Fightingbox/Flatbox-LED-Mirrored/pictures/assets/5.jpg

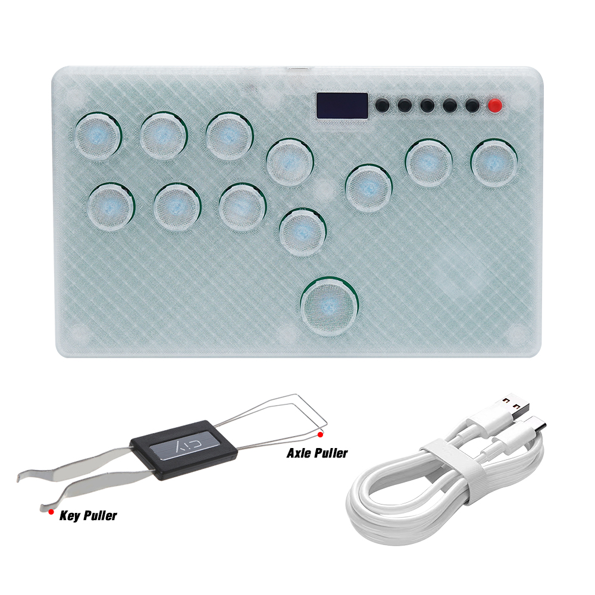
pictures/assets/5.jpg
