Fightingbox/Flatbox-LED-Mirrored/software/configs/BentoBox/assets/ScrubTier_Large.png

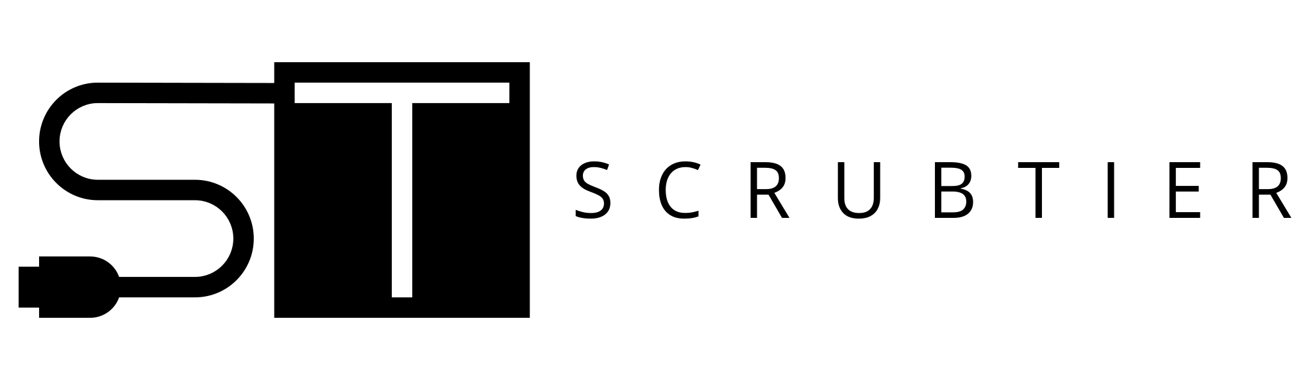
software/configs/BentoBox/assets/ScrubTier_Large.png
