Fightingbox/Flatbox-LED-Mirrored/software/configs/BentoBox/assets/ST_BentoBoxV1.png

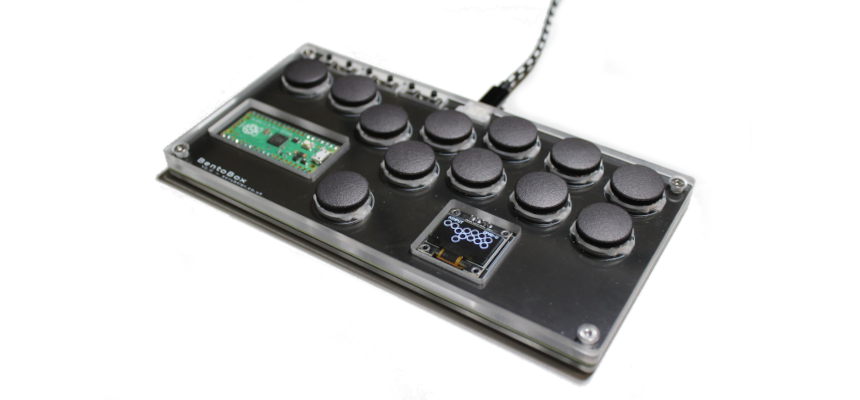
software/configs/BentoBox/assets/ST_BentoBoxV1.png
