Fightingbox/Flatbox-LED-Mirrored/software/configs/BentoBox/assets/ST_BentoBoxV2.png

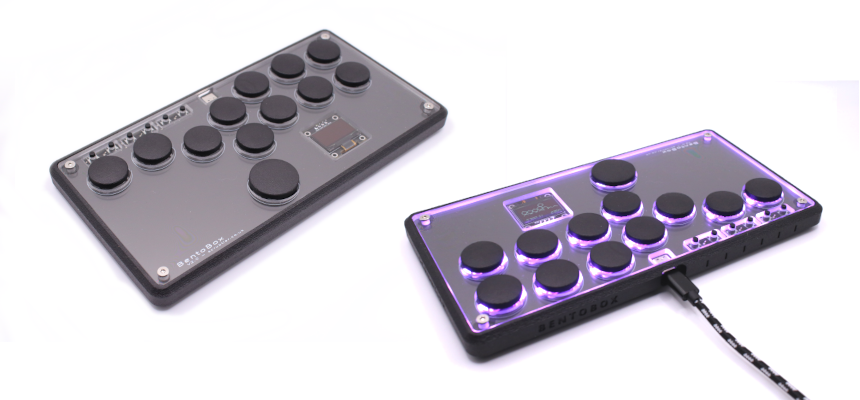
software/configs/BentoBox/assets/ST_BentoBoxV2.png
