Fightingbox/Flatbox-LED-Mirrored/software/configs/BentoBox/assets/ST_GGEZStick.png

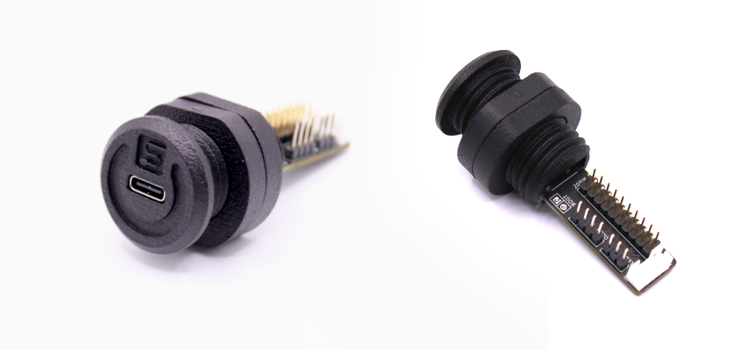
software/configs/BentoBox/assets/ST_GGEZStick.png
