Fightingbox/Flatbox-LED-Mirrored/software/configs/DuelPad-S001/assets/Flatbox-rev2b-finished-product.jpg

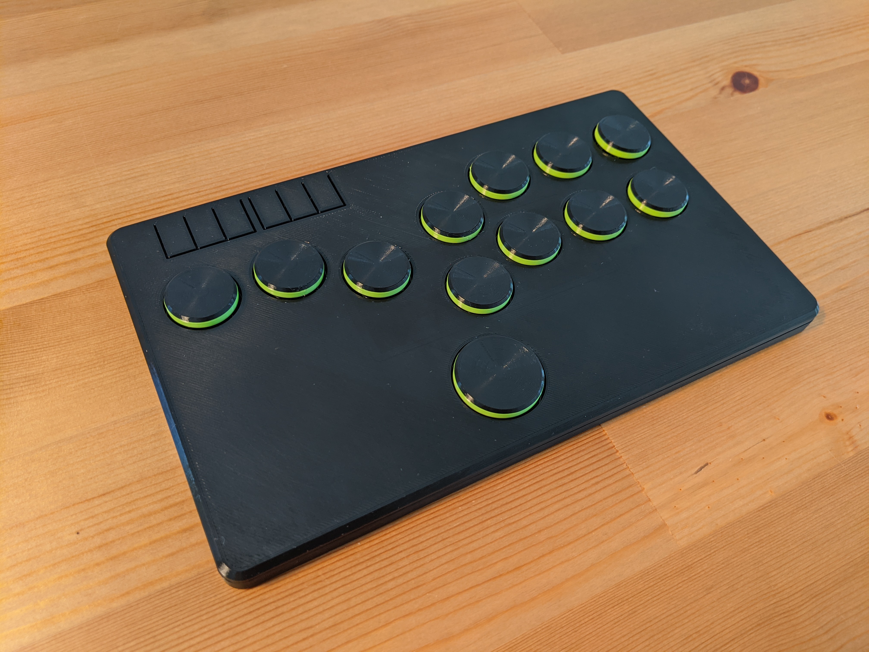
software/configs/DuelPad-S001/assets/Flatbox-rev2b-finished-product.jpg
