Fightingbox/Flatbox-LED-Mirrored/software/configs/FightboardV3/assets/FightboardV3.jpg

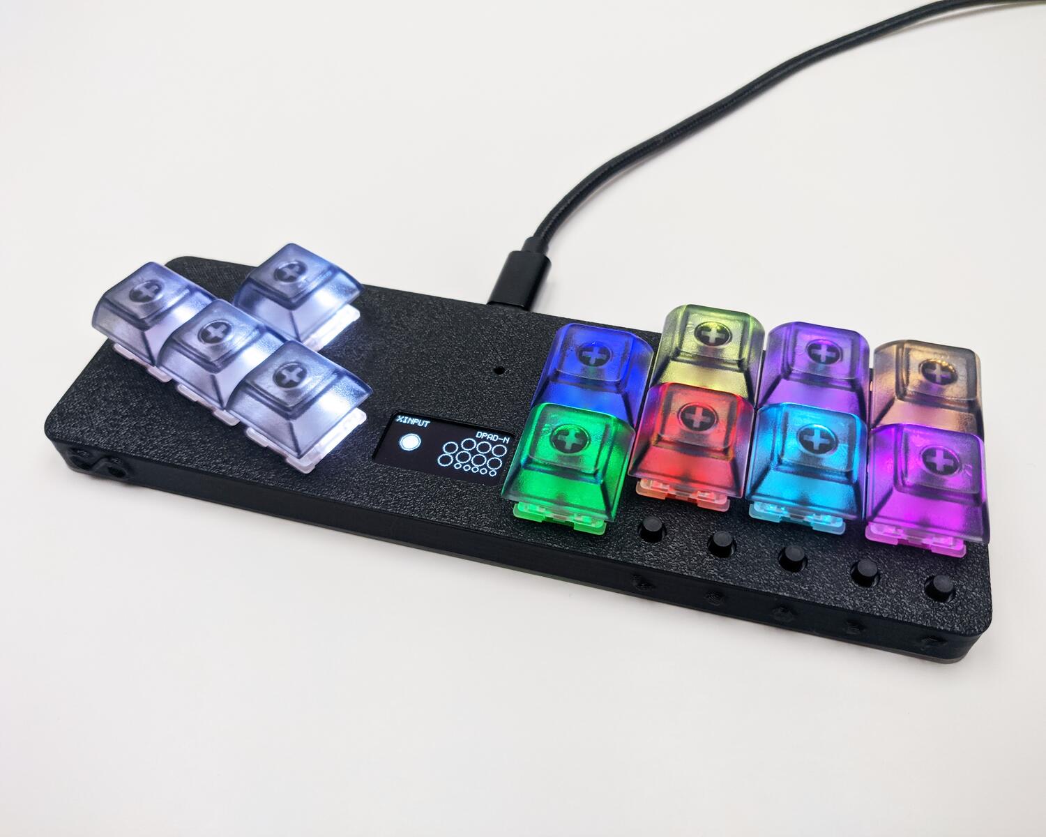
software/configs/FightboardV3/assets/FightboardV3.jpg
