Fightingbox/Flatbox-LED-Mirrored/software/configs/FightboardV3Mirrored/assets/FightboardV3Mirrored.jpg

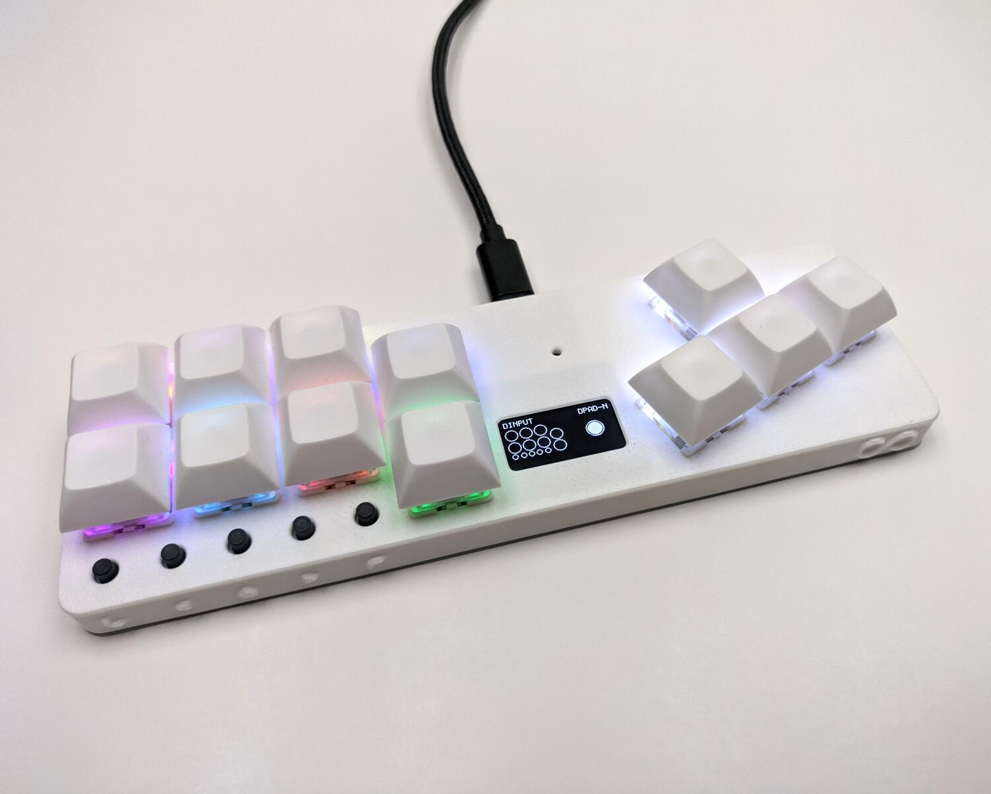
software/configs/FightboardV3Mirrored/assets/FightboardV3Mirrored.jpg
