Fightingbox/Flatbox-LED-Mirrored/software/configs/FlatboxRev5/assets/Flatbox-rev5.jpg

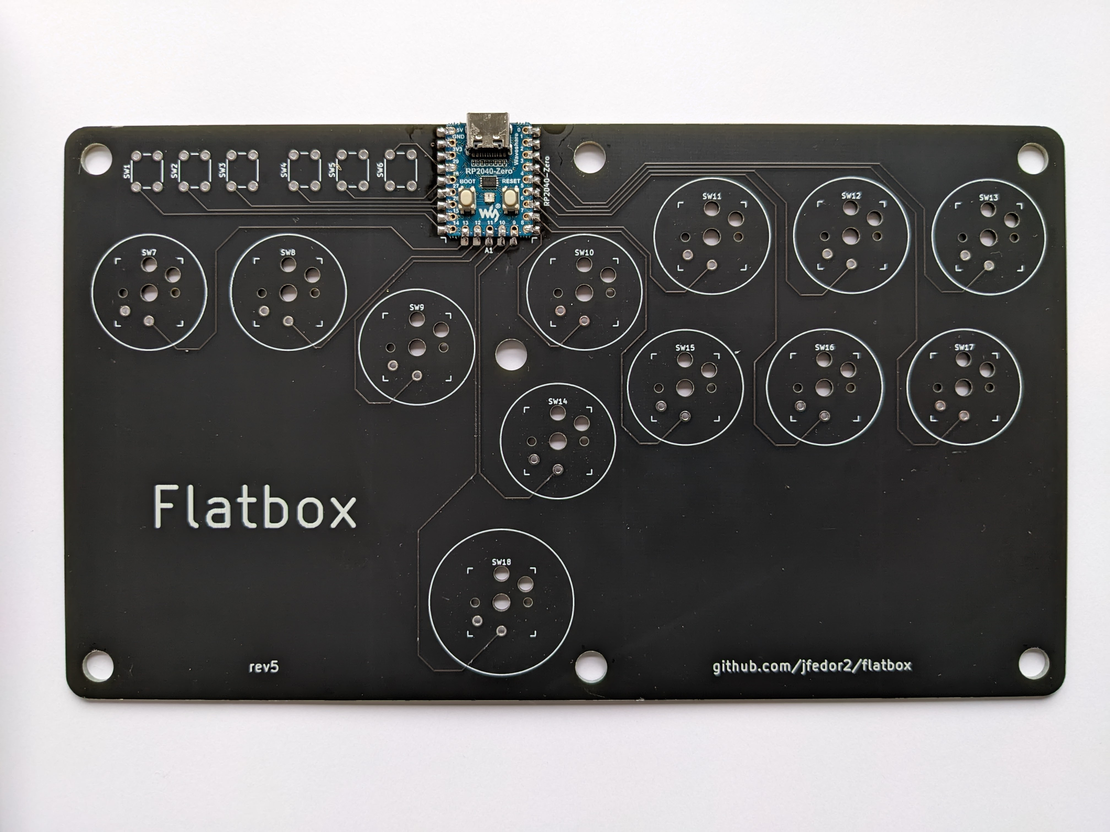
software/configs/FlatboxRev5/assets/Flatbox-rev5.jpg
