Fightingbox/Flatbox-LED-Mirrored/software/configs/FlatboxRev5RGB/assets/Flatbox-rev5-rgb.jpg

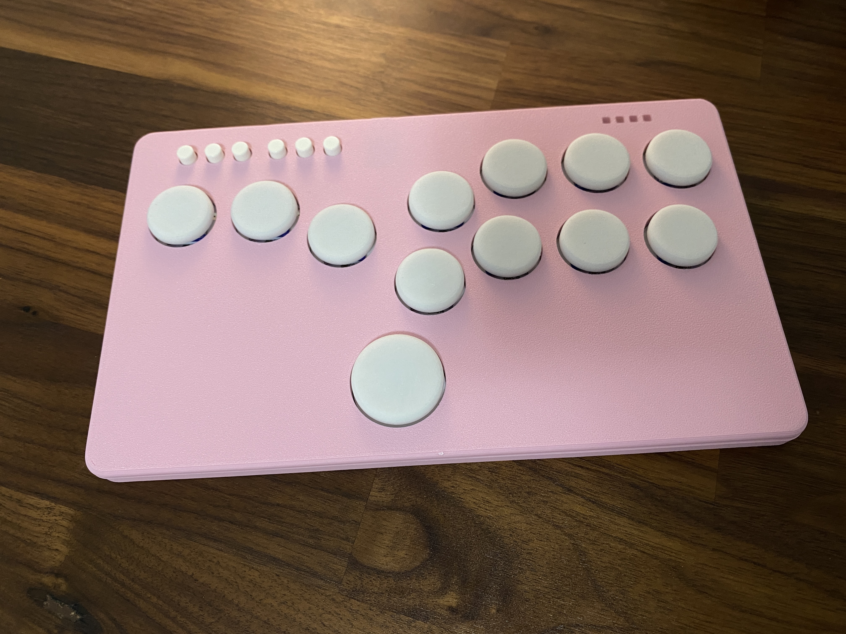
software/configs/FlatboxRev5RGB/assets/Flatbox-rev5-rgb.jpg
