Fightingbox/Flatbox-LED-Mirrored/software/configs/FlatboxRev5Southpaw/assets/Flatbox-rev5.jpg

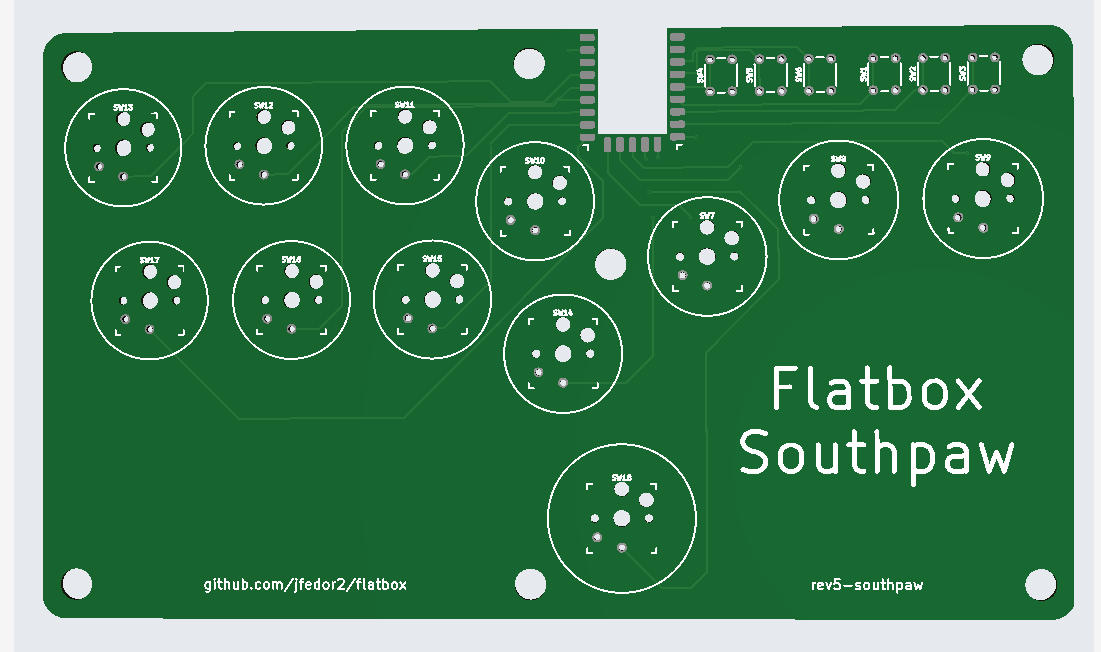
software/configs/FlatboxRev5Southpaw/assets/Flatbox-rev5.jpg
