Fightingbox/Flatbox-LED-Mirrored/software/configs/Haute42/assets/Haute42_G12.png

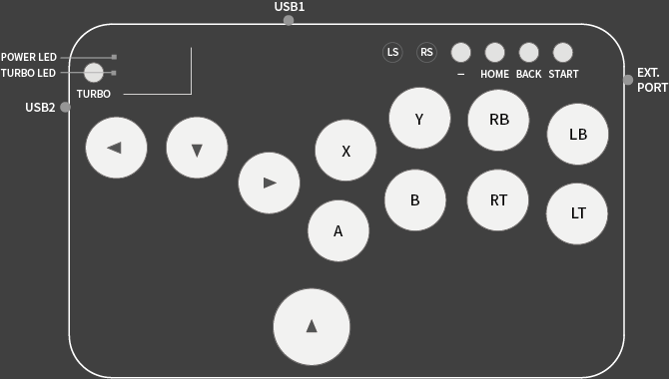
software/configs/Haute42/assets/Haute42_G12.png
