Fightingbox/Flatbox-LED-Mirrored/software/configs/Haute42/assets/Haute42_G13.png

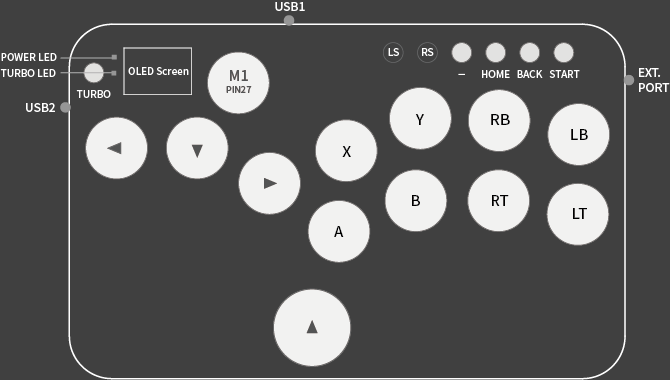
software/configs/Haute42/assets/Haute42_G13.png
