Fightingbox/Flatbox-LED-Mirrored/software/configs/Haute42/assets/Haute42_G16.png

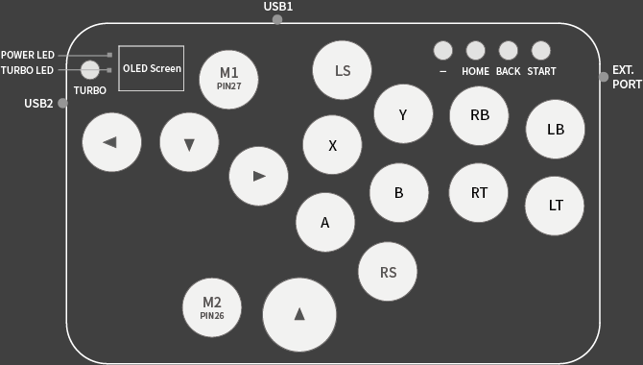
software/configs/Haute42/assets/Haute42_G16.png
