Fightingbox/Flatbox-LED-Mirrored/software/configs/Haute42/assets/Haute42_G_series.png

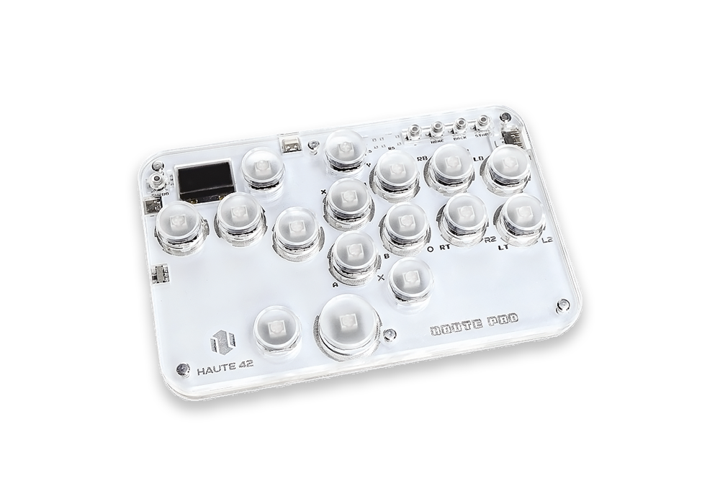
software/configs/Haute42/assets/Haute42_G_series.png
