Fightingbox/Flatbox-LED-Mirrored/software/configs/Haute42/assets/Haute42_Mini.png

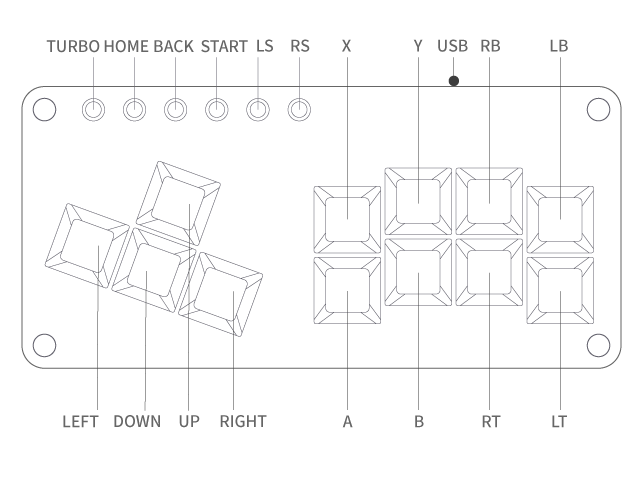
software/configs/Haute42/assets/Haute42_Mini.png
