Fightingbox/Flatbox-LED-Mirrored/software/configs/Haute42/assets/Haute42_T16.png

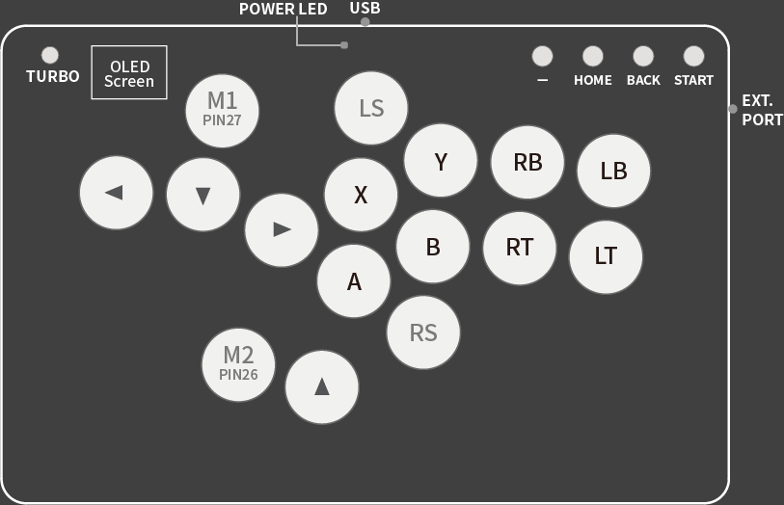
software/configs/Haute42/assets/Haute42_T16.png
