Fightingbox/Flatbox-LED-Mirrored/software/configs/Haute42/assets/Haute42_T_series.png

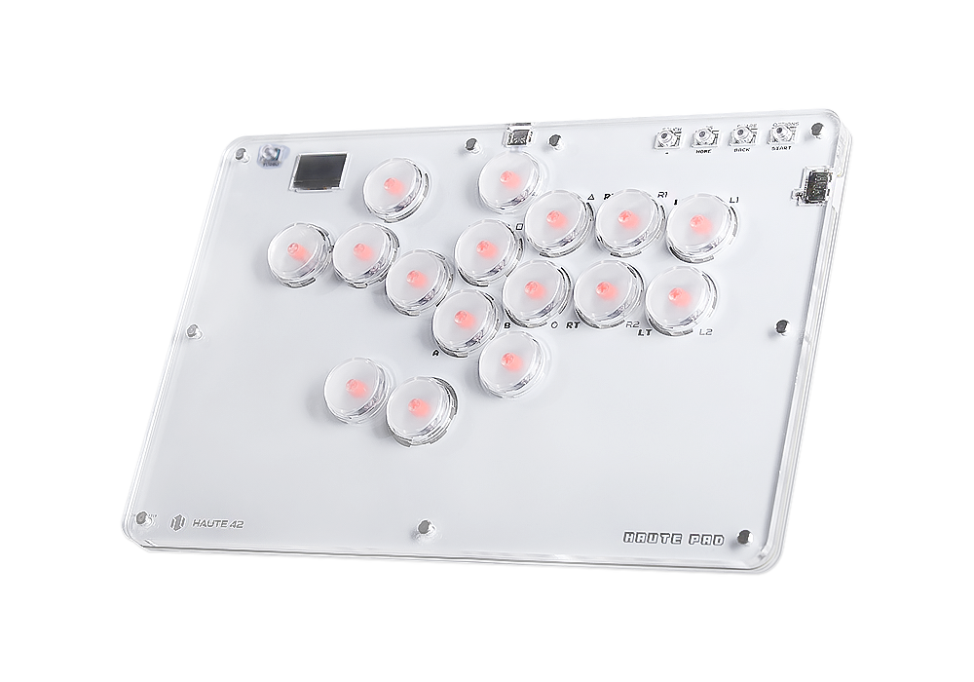
software/configs/Haute42/assets/Haute42_T_series.png
