Fightingbox/Flatbox-LED-Mirrored/software/configs/KB2040/assets/PinMapping.png

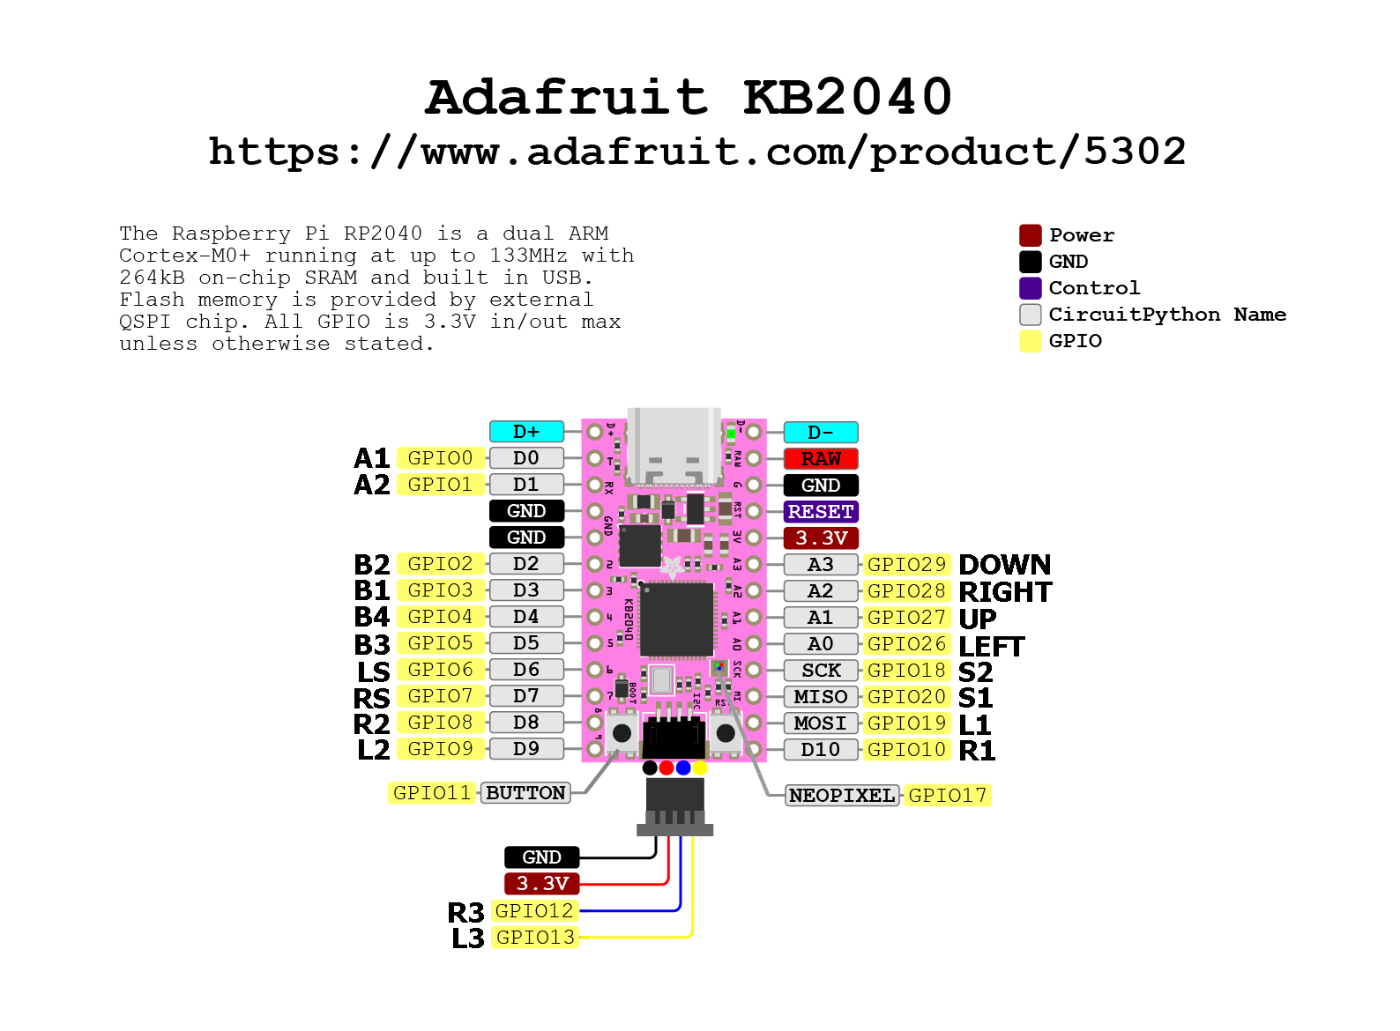
software/configs/KB2040/assets/PinMapping.png
