Fightingbox/Flatbox-LED-Mirrored/software/configs/KeyboardConverter/assets/WaveshareRP2040Zero.png

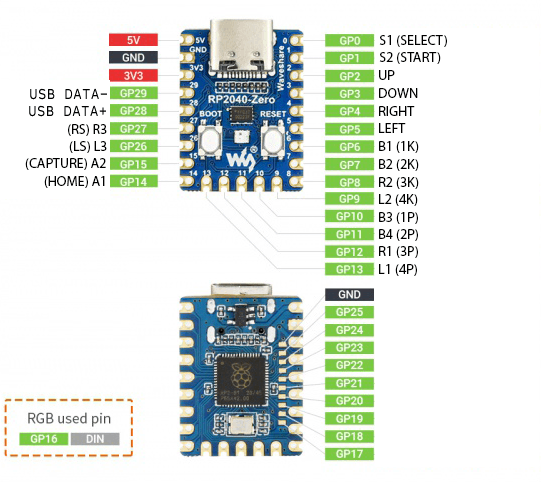
software/configs/KeyboardConverter/assets/WaveshareRP2040Zero.png
