Fightingbox/Flatbox-LED-Mirrored/software/configs/Liatris/assets/Liatris.png

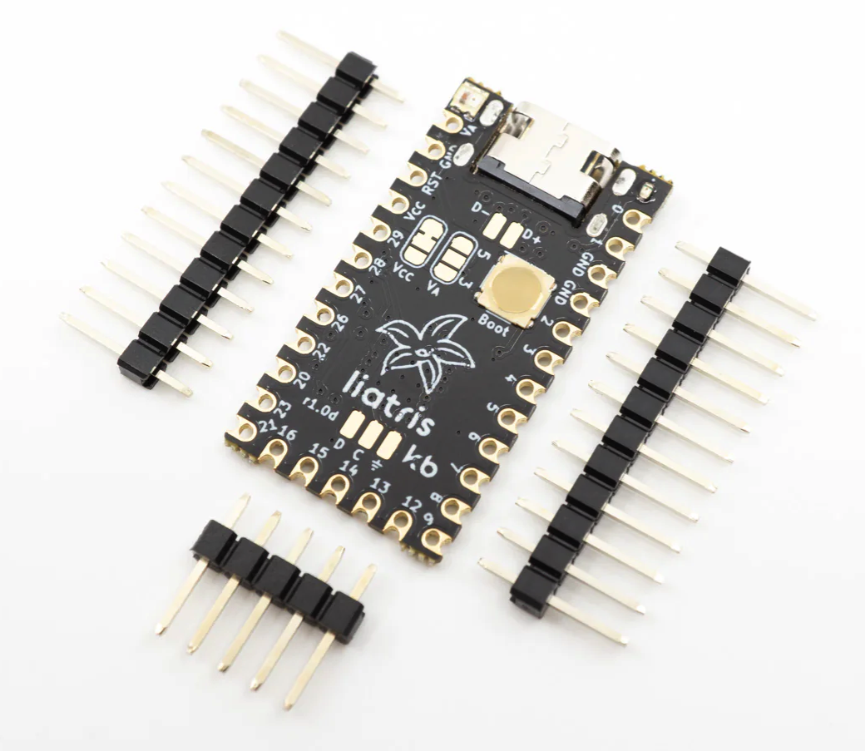
software/configs/Liatris/assets/Liatris.png
