Fightingbox/Flatbox-LED-Mirrored/software/configs/Mavercade/assets/keebfighter-00.png

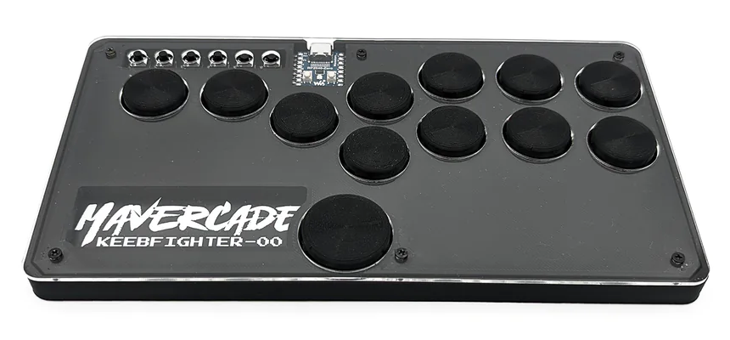
software/configs/Mavercade/assets/keebfighter-00.png
