Fightingbox/Flatbox-LED-Mirrored/software/configs/Mavercade/assets/keebfighter-01.png

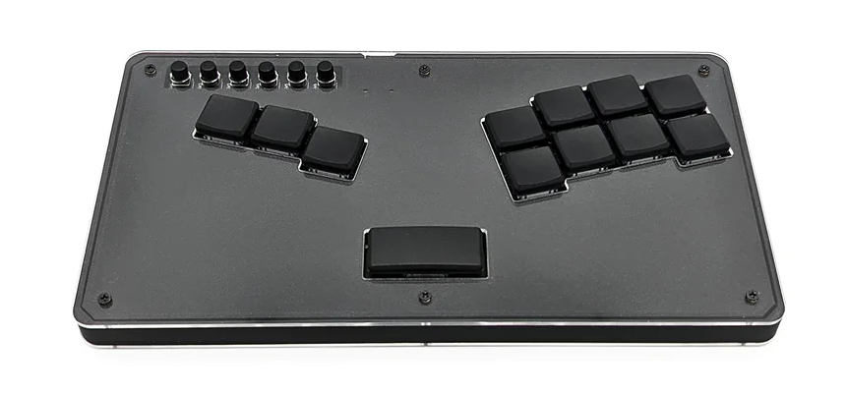
software/configs/Mavercade/assets/keebfighter-01.png
