Fightingbox/Flatbox-LED-Mirrored/software/configs/Mavercade/assets/keebfighter-02.png

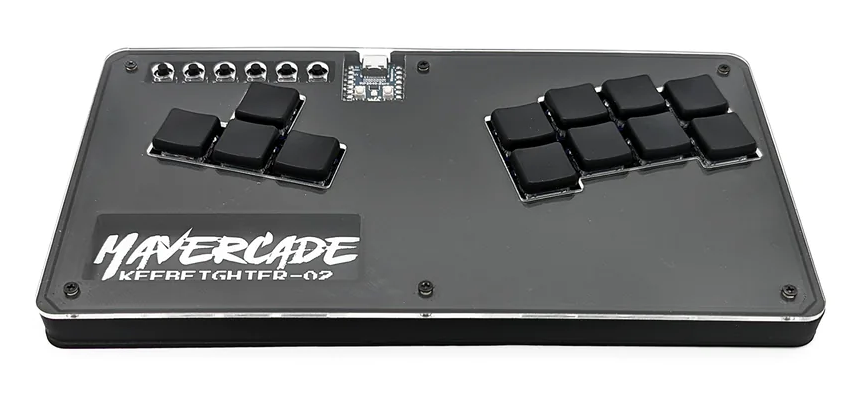
software/configs/Mavercade/assets/keebfighter-02.png
