Fightingbox/Flatbox-LED-Mirrored/software/configs/OpenCore0/assets/Open_Core0_WASD.jpg

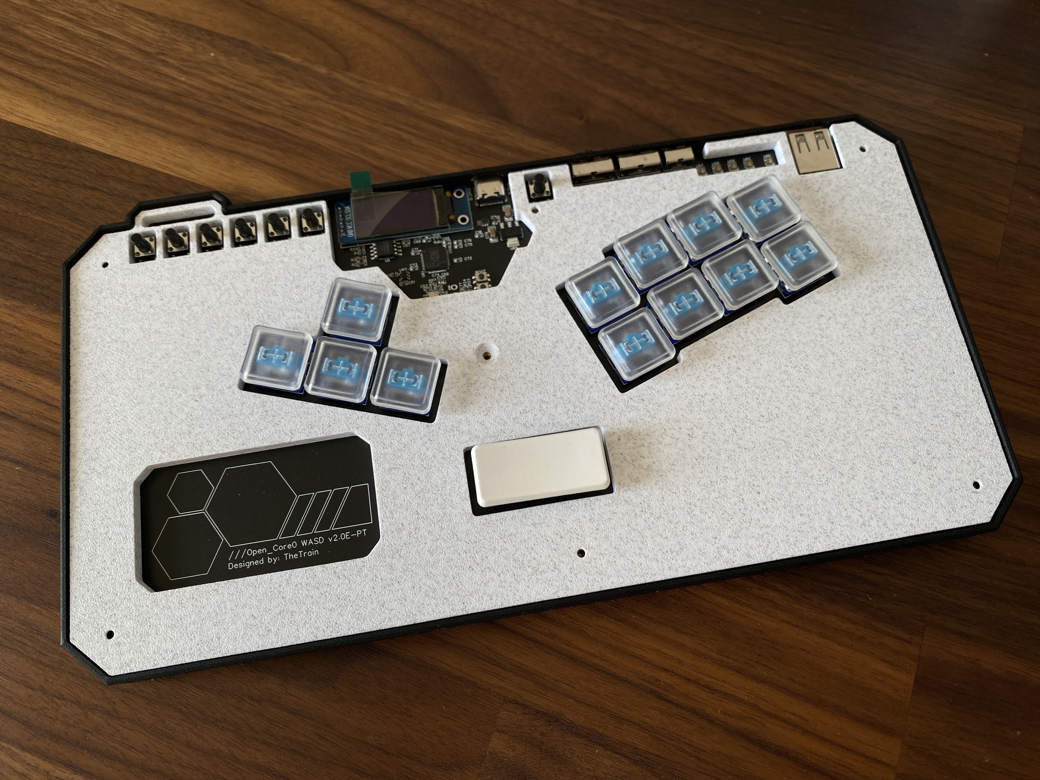
software/configs/OpenCore0/assets/Open_Core0_WASD.jpg
