Fightingbox/Flatbox-LED-Mirrored/software/configs/OpenCore0/assets/Open_Core0_WASD_pinout.png

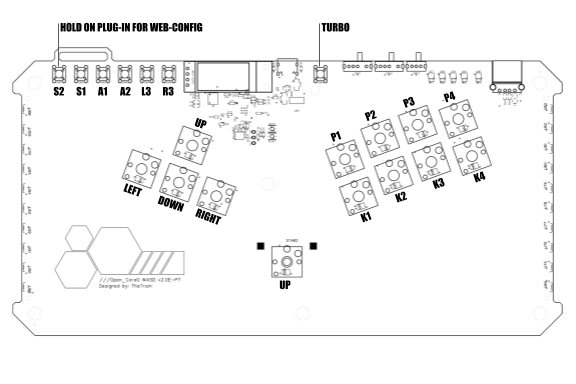
software/configs/OpenCore0/assets/Open_Core0_WASD_pinout.png
