Fightingbox/Flatbox-LED-Mirrored/software/configs/Pico/assets/PinMapping.png

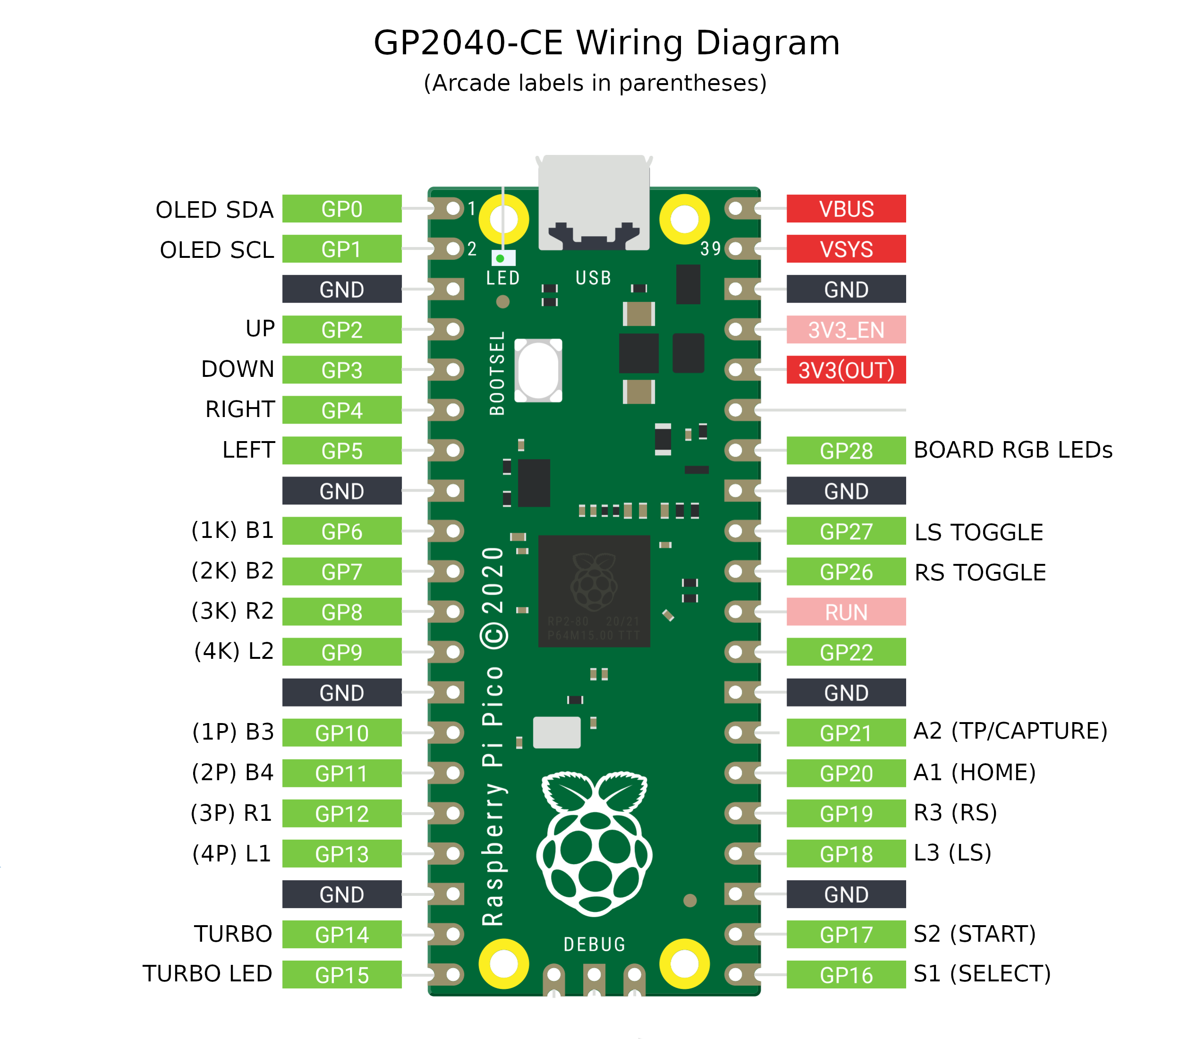
software/configs/Pico/assets/PinMapping.png
