Fightingbox/Flatbox-LED-Mirrored/software/configs/PicoFightingBoard/assets/PicoFightingBoard_v1.1.jpg

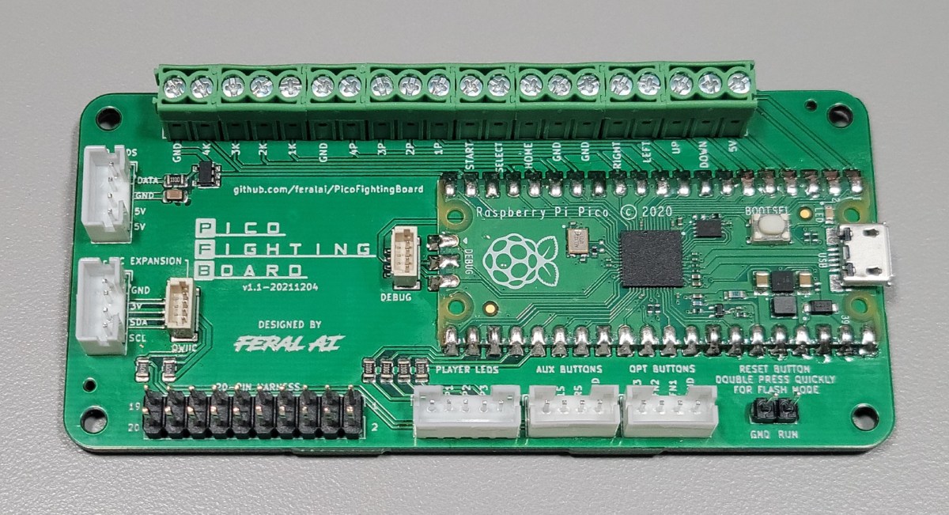
software/configs/PicoFightingBoard/assets/PicoFightingBoard_v1.1.jpg
