Fightingbox/Flatbox-LED-Mirrored/software/configs/RanaTadpole/assets/RanaTadpole1.jpg

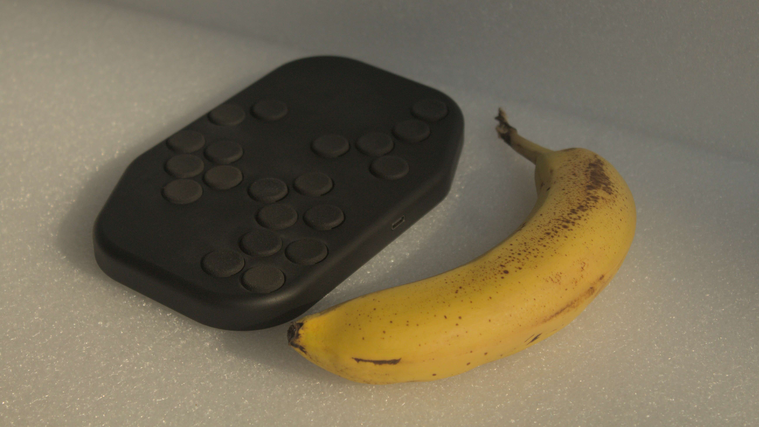
software/configs/RanaTadpole/assets/RanaTadpole1.jpg
