Fightingbox/Flatbox-LED-Mirrored/software/configs/RanaTadpole/assets/RanaTadpole2.jpg

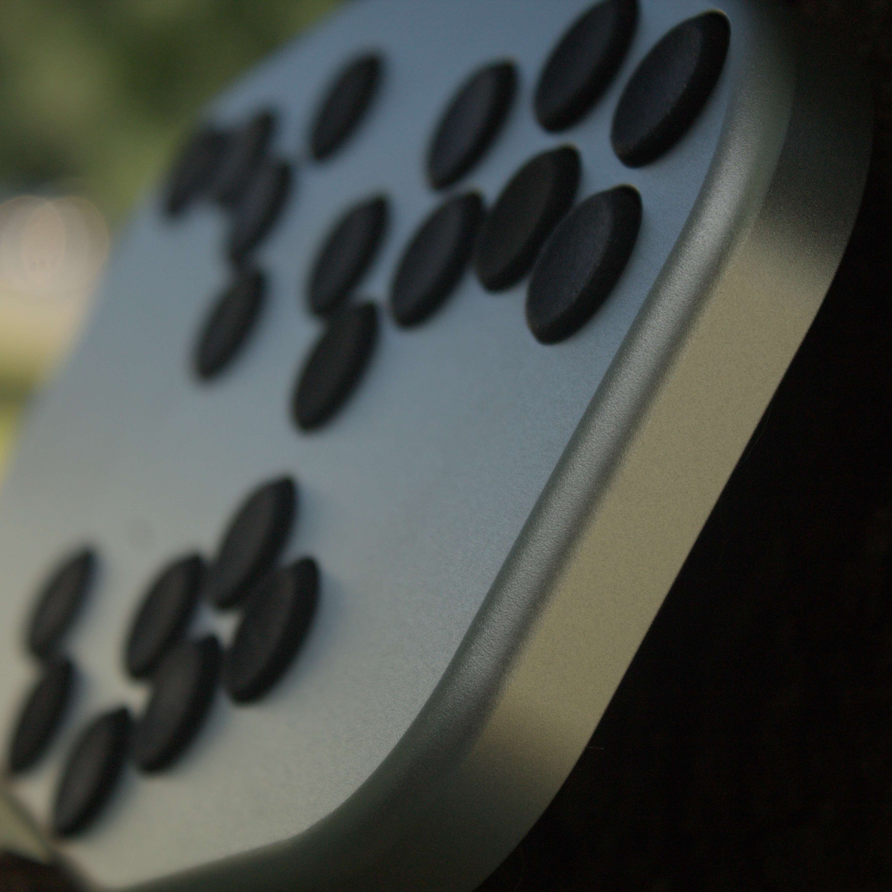
software/configs/RanaTadpole/assets/RanaTadpole2.jpg
