Fightingbox/Flatbox-LED-Mirrored/software/configs/RanaTadpole/assets/RanaTadpole_buttons.png

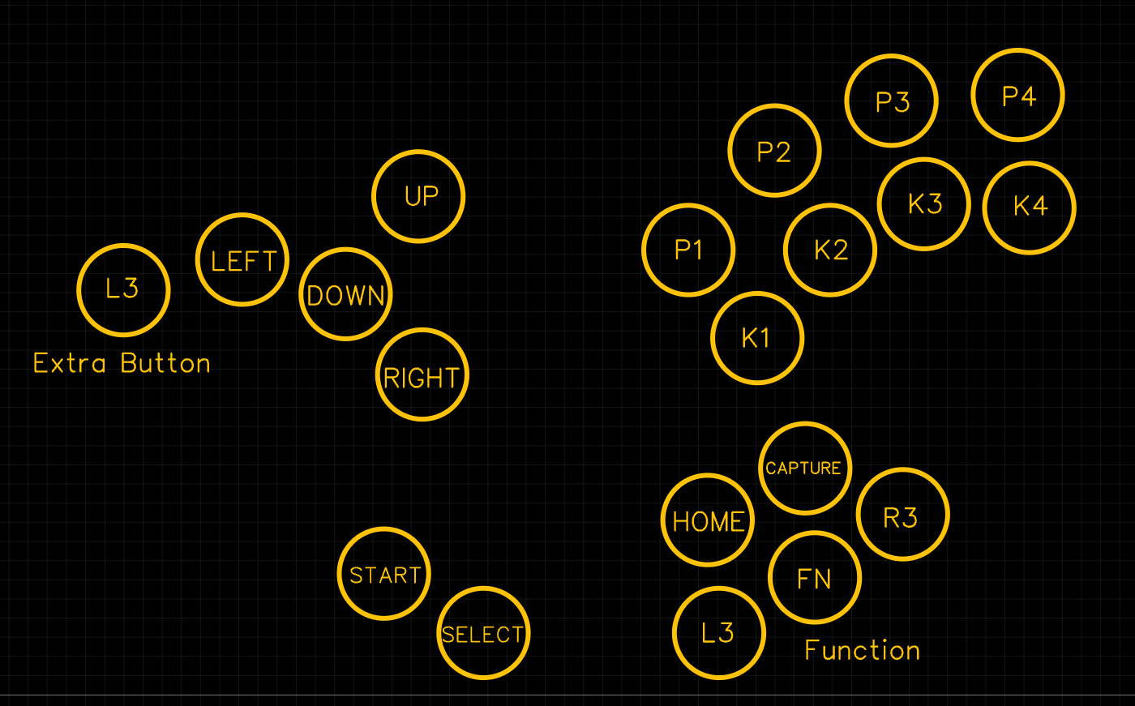
software/configs/RanaTadpole/assets/RanaTadpole_buttons.png
