Fightingbox/Flatbox-LED-Mirrored/software/configs/ReflexEncodeV2.0/assets/ReflexBoard_V2.png

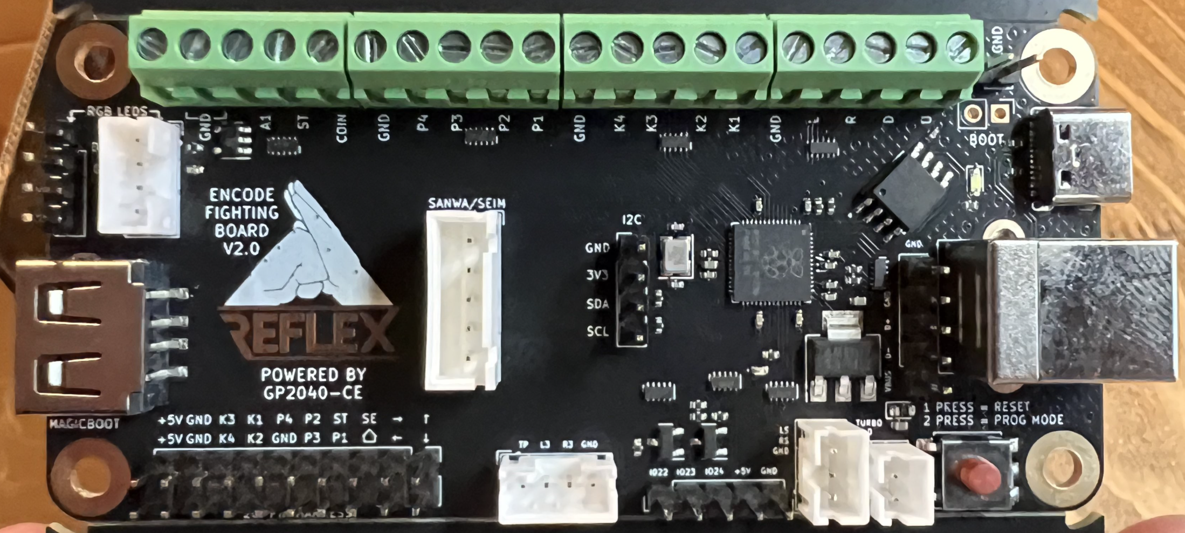
software/configs/ReflexEncodeV2.0/assets/ReflexBoard_V2.png
