Fightingbox/Flatbox-LED-Mirrored/software/configs/RP2040AdvancedBreakoutBoard/assets/RP2040AdvancedBreakoutBoard.jpg

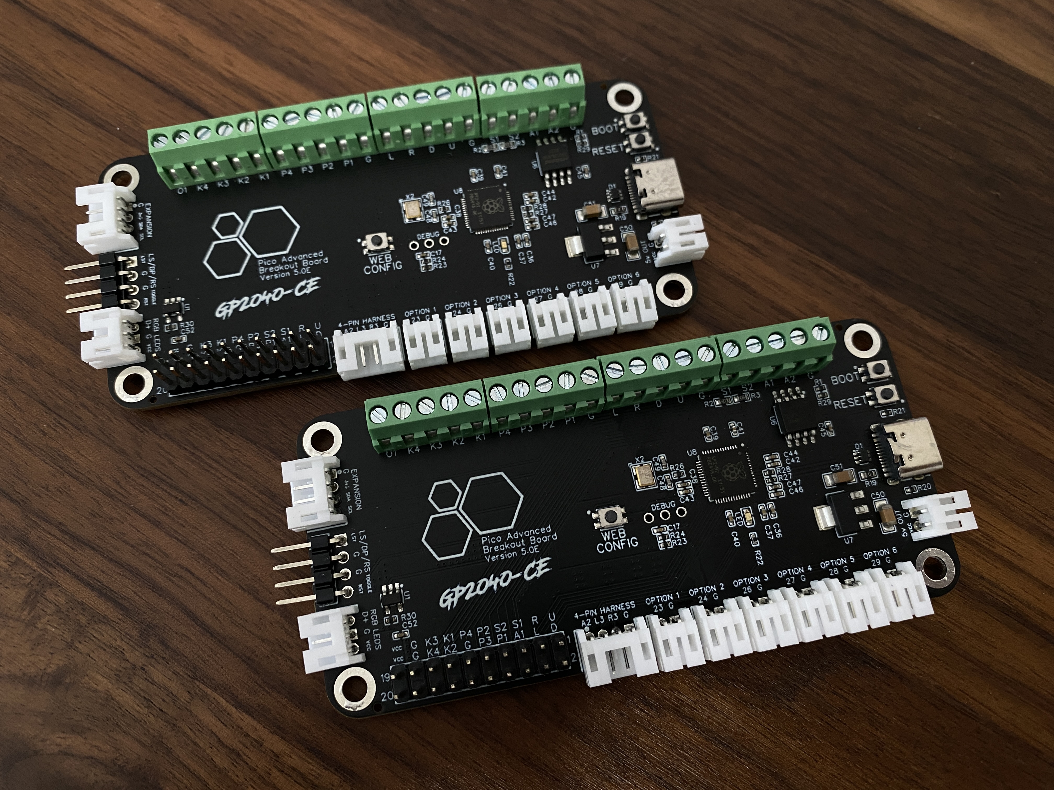
software/configs/RP2040AdvancedBreakoutBoard/assets/RP2040AdvancedBreakoutBoard.jpg
