Fightingbox/Flatbox-LED-Mirrored/software/configs/RP2040AdvancedBreakoutBoard/assets/RP2040AdvancedBreakoutBoard_pinout.png

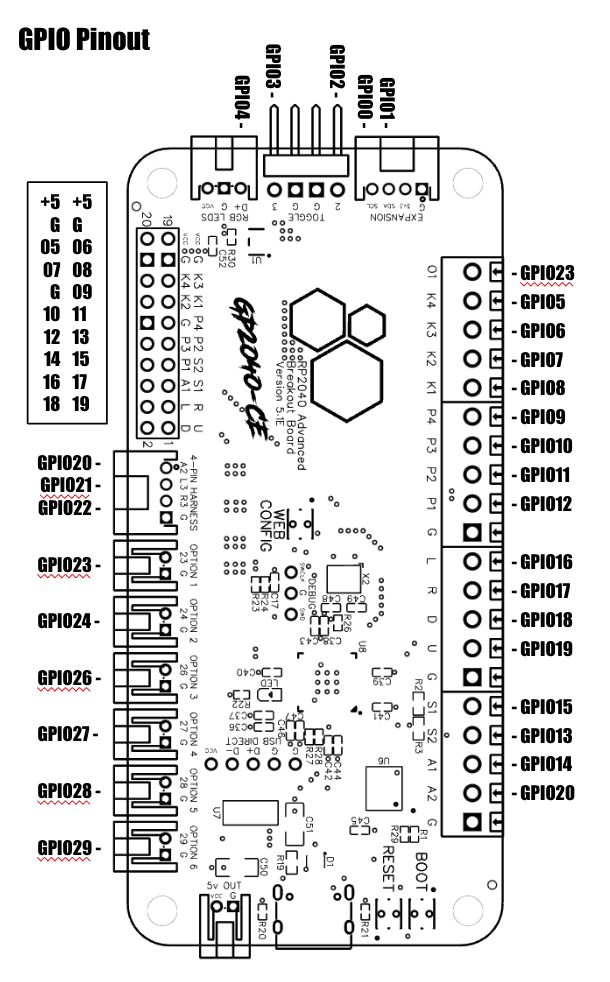
software/configs/RP2040AdvancedBreakoutBoard/assets/RP2040AdvancedBreakoutBoard_pinout.png
