Fightingbox/Flatbox-LED-Mirrored/software/configs/RP2040AdvancedBreakoutBoardUSBPassthrough/assets/RP2040 Advanced Breakout Board - Passthrough.jpg

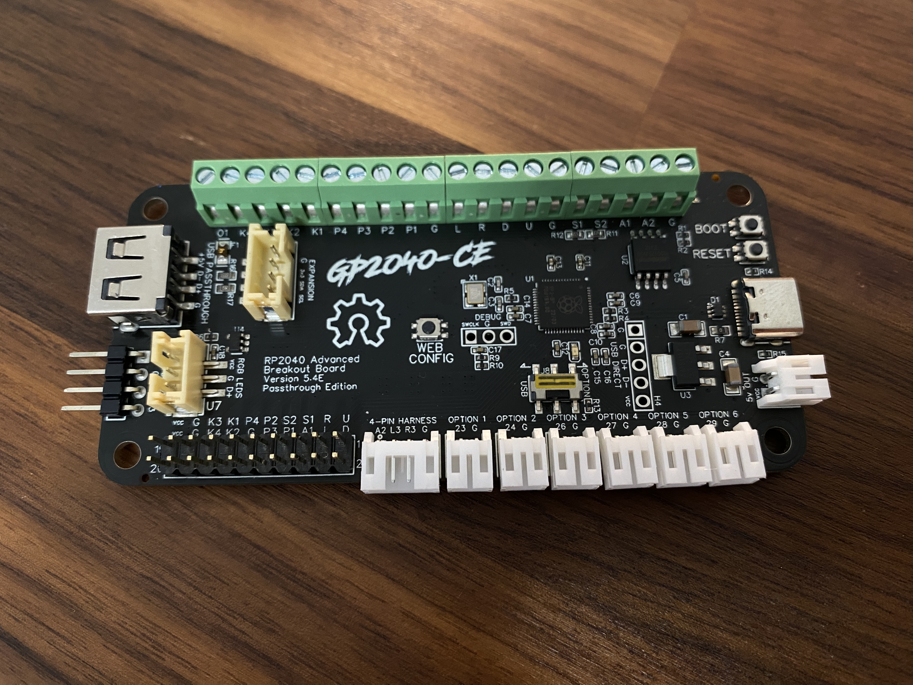
software/configs/RP2040AdvancedBreakoutBoardUSBPassthrough/assets/RP2040 Advanced Breakout Board - Passthrough.jpg
