Fightingbox/Flatbox-LED-Mirrored/software/configs/RP2040MiniBreakoutBoard/assets/RP2040MiniBreakoutBoard.jpg

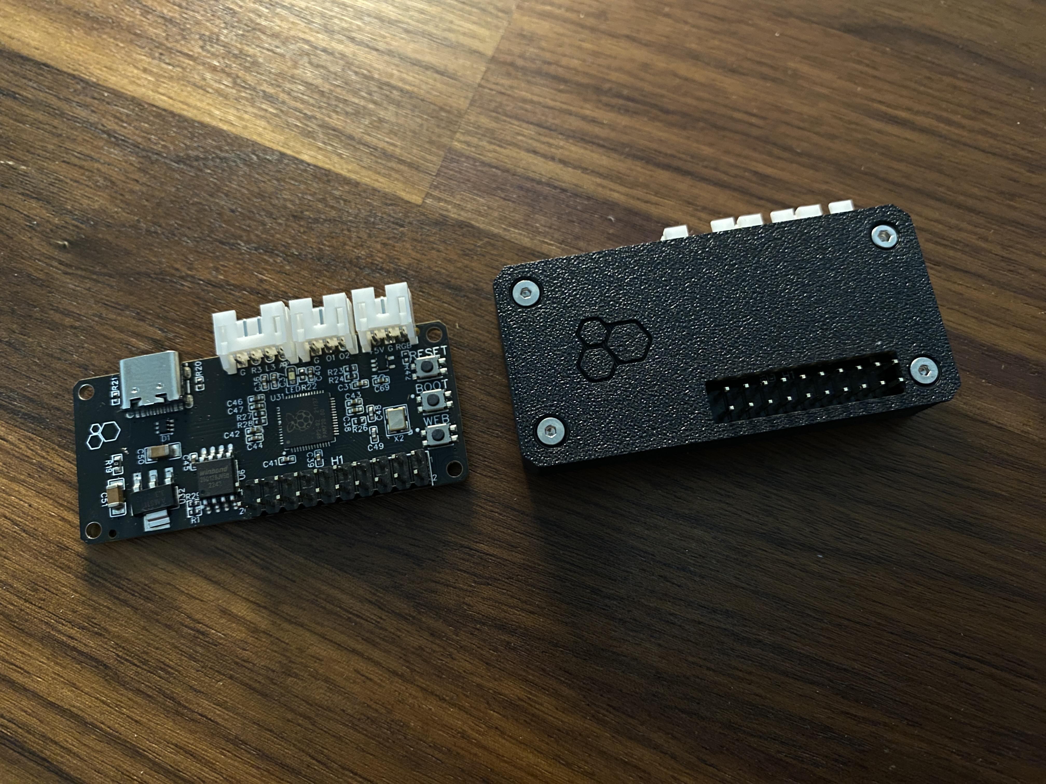
software/configs/RP2040MiniBreakoutBoard/assets/RP2040MiniBreakoutBoard.jpg
