Fightingbox/Flatbox-LED-Mirrored/software/configs/SGFBridget/assets/SGF_Bridget.png

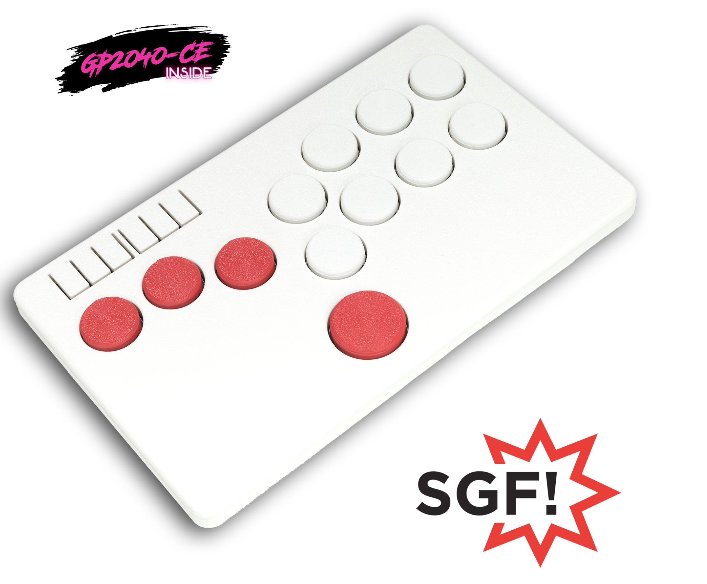
software/configs/SGFBridget/assets/SGF_Bridget.png
