Fightingbox/Flatbox-LED-Mirrored/software/configs/SGFBridget/assets/SGF_Bridget_Layout.jpg

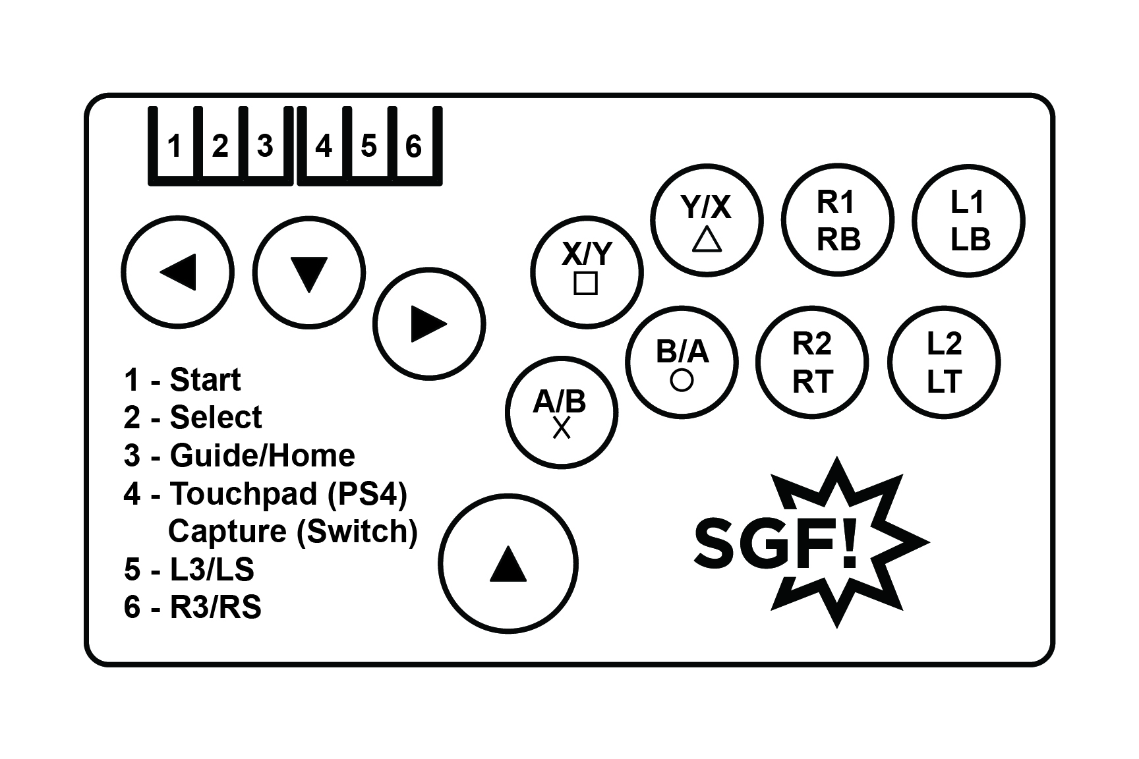
software/configs/SGFBridget/assets/SGF_Bridget_Layout.jpg
