Fightingbox/Flatbox-LED-Mirrored/software/configs/SGFFaust/assets/SGF_Faust.png

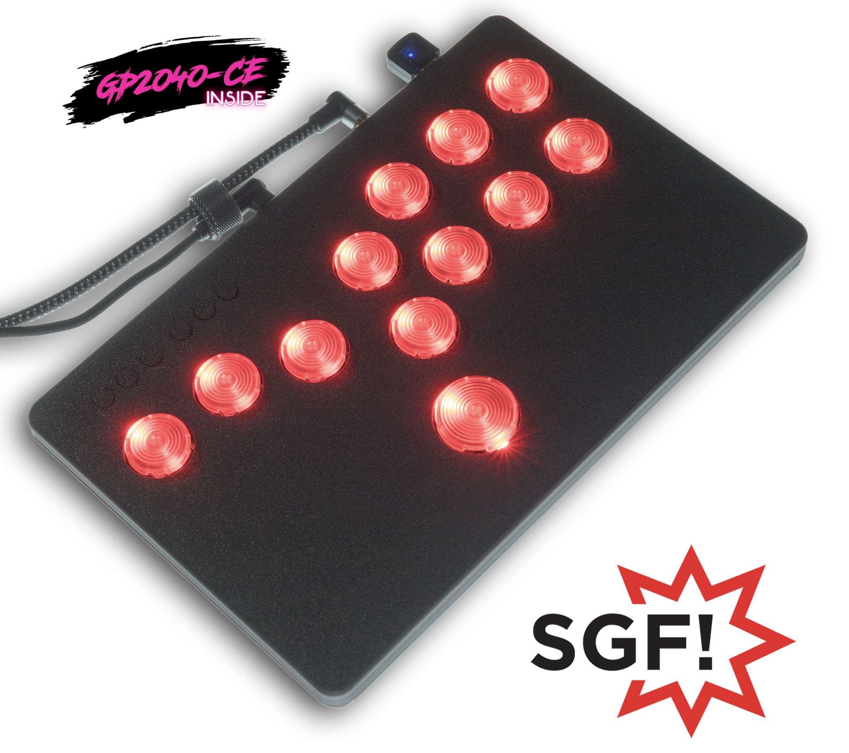
software/configs/SGFFaust/assets/SGF_Faust.png
