Fightingbox/Flatbox-LED-Mirrored/software/configs/SGFFaust/assets/SGF_Faust_Layout.png

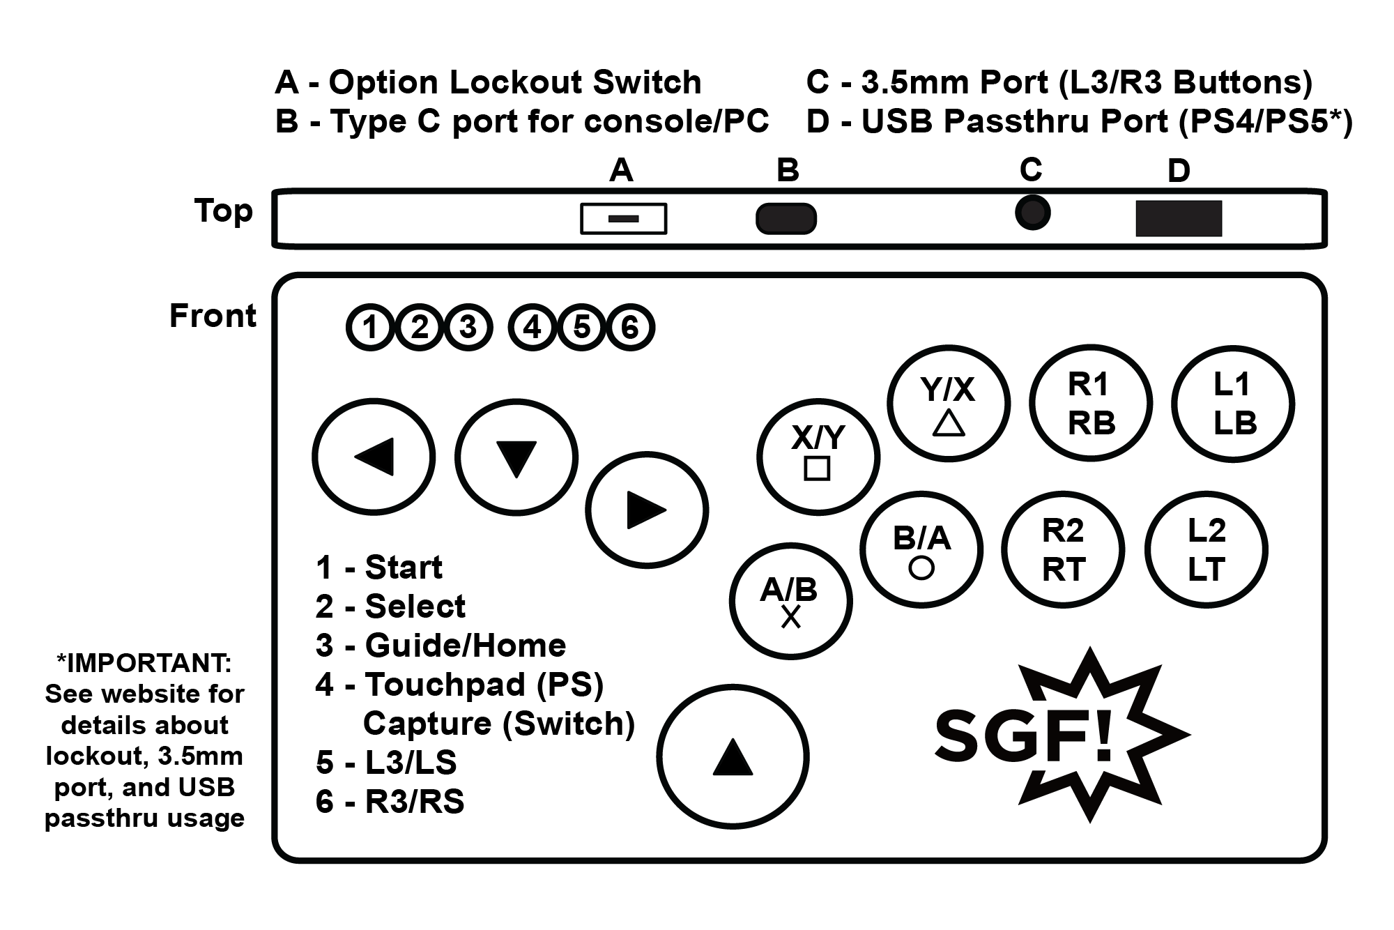
software/configs/SGFFaust/assets/SGF_Faust_Layout.png
