Fightingbox/Flatbox-LED-Mirrored/software/configs/SparkFunProMicro/assets/SparkFunProMicroRP2040.png

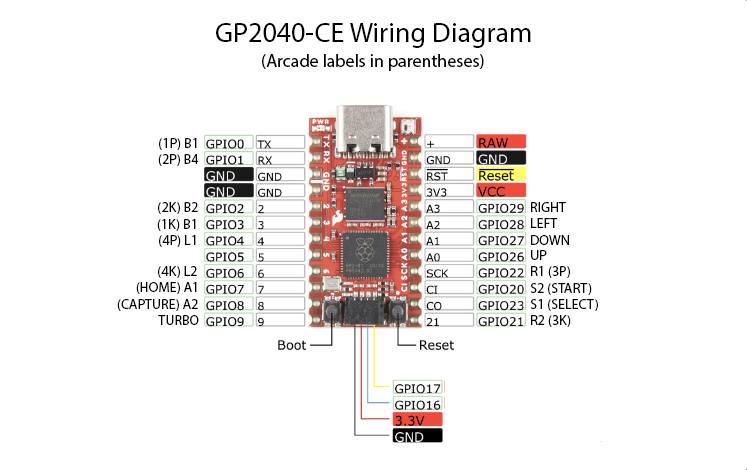
software/configs/SparkFunProMicro/assets/SparkFunProMicroRP2040.png
