Fightingbox/Flatbox-LED-Mirrored/software/configs/Stress/assets/stress-00.jpg

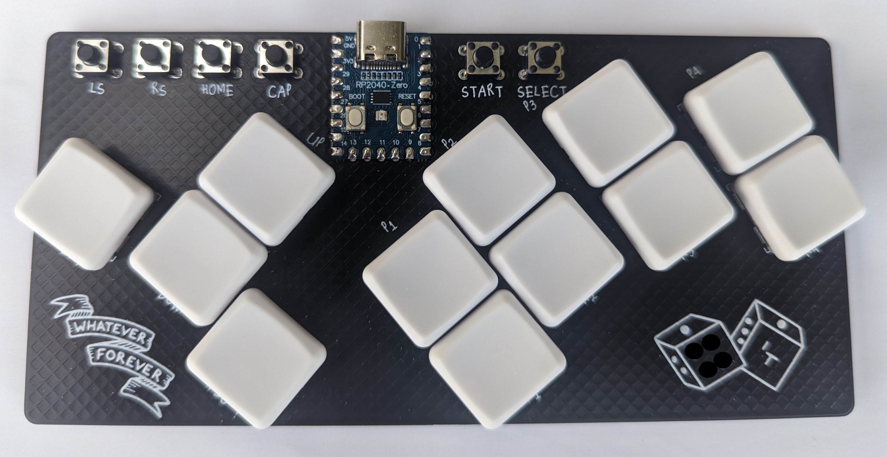
software/configs/Stress/assets/stress-00.jpg
