Fightingbox/Flatbox-LED-Mirrored/software/www/assets/rp2040.png

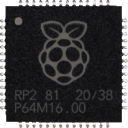
software/www/assets/rp2040.png
